NisipeanuAlexandru/Oscilator-RC-cu-Punte-Wien/Simulations/stabilitate(AC).jpg

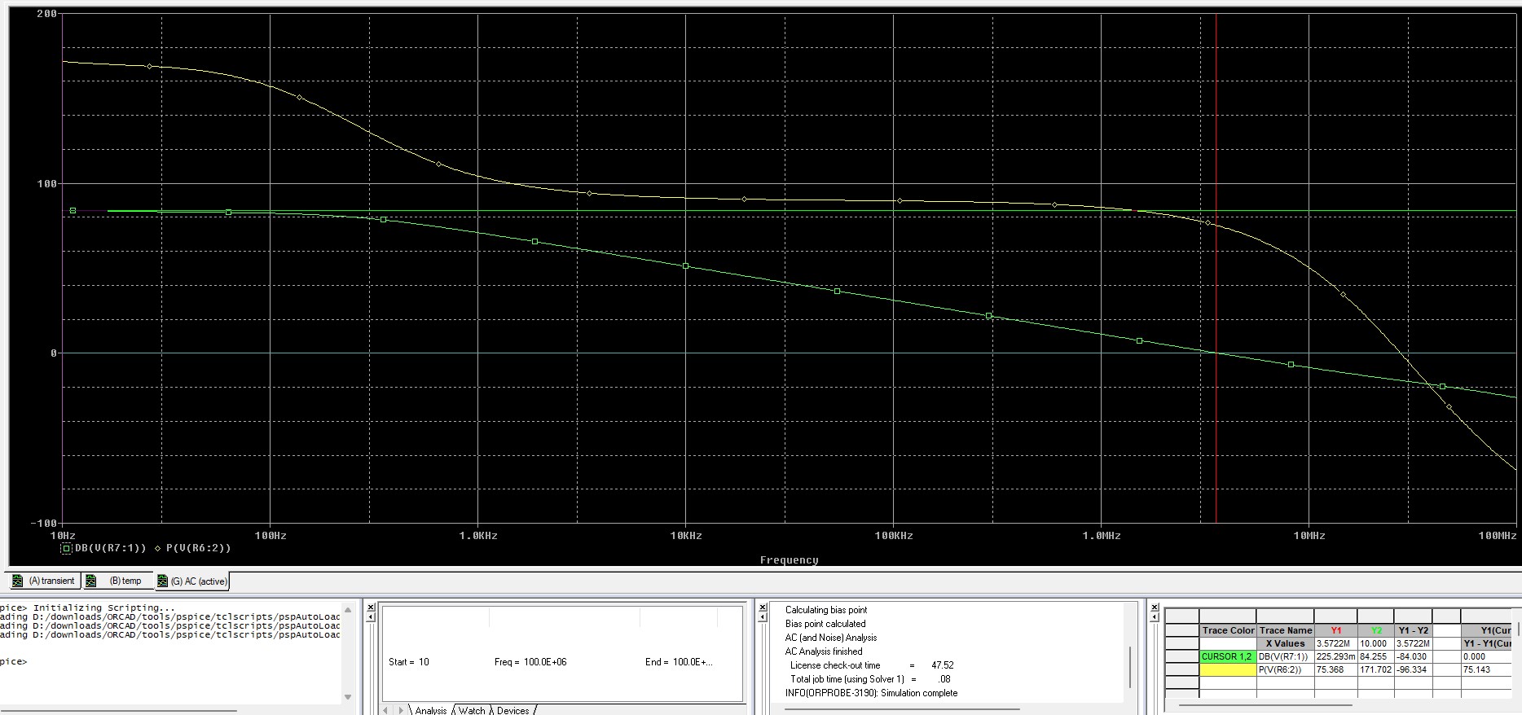
Simulations/stabilitate(AC).jpg
