NisipeanuAlexandru/Oscilator-RC-cu-Punte-Wien/Simulations/stabilitate(AC)_-20_120.jpg

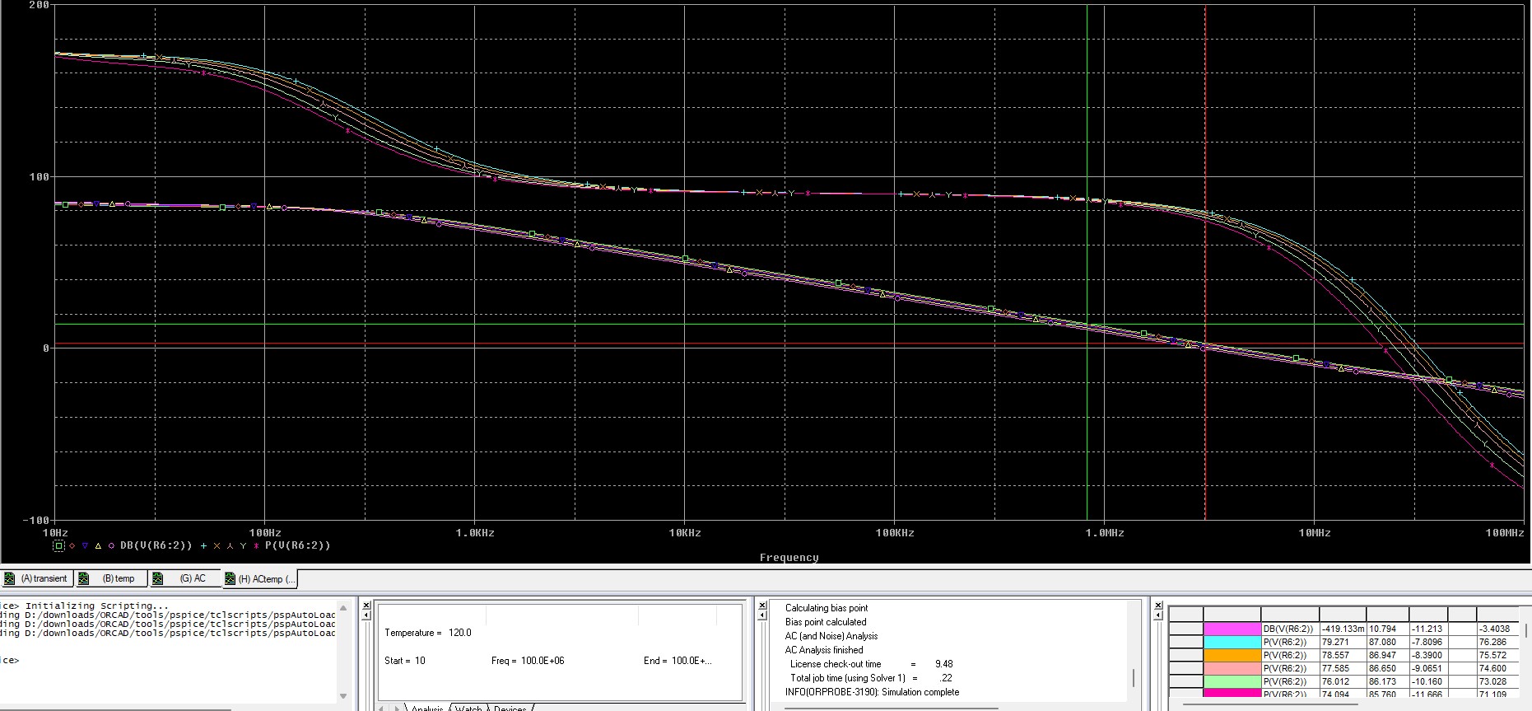
Simulations/stabilitate(AC)_-20_120.jpg
