NisipeanuAlexandru/Oscilator-RC-cu-Punte-Wien/Simulations/transient(zoom)_45KHz.jpg

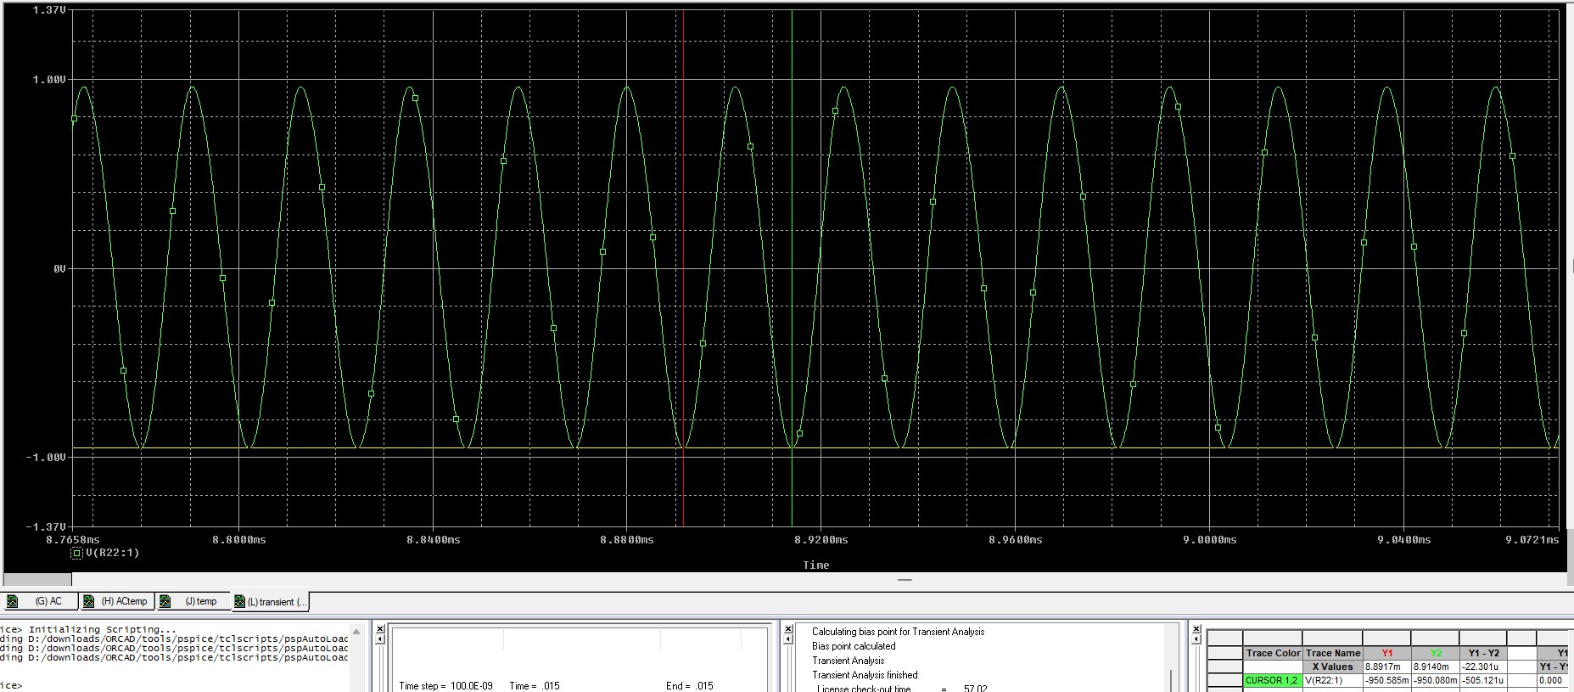
Simulations/transient(zoom)_45KHz.jpg
