NisipeanuAlexandru/Oscilator-RC-cu-Punte-Wien/Simulations/transient_7.7KHz.jpg

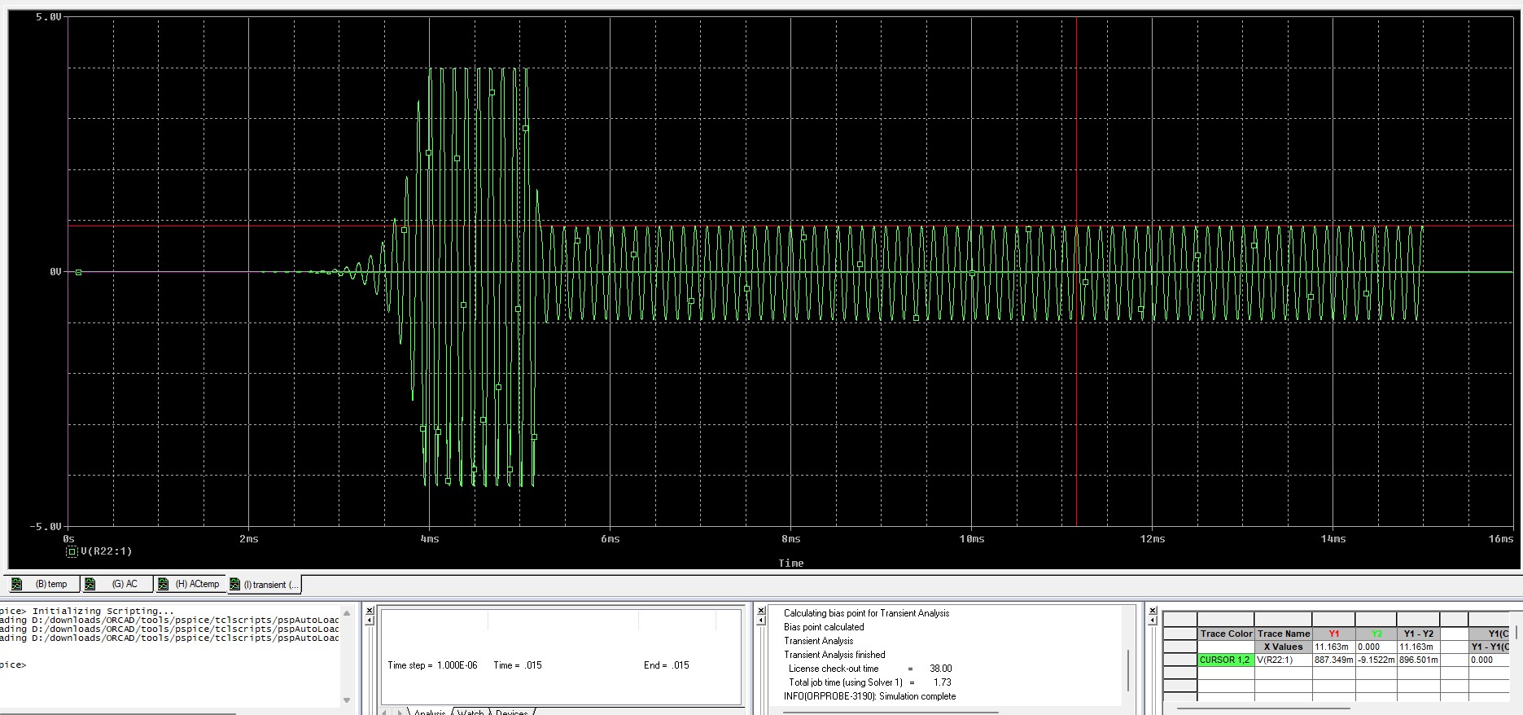
Simulations/transient_7.7KHz.jpg
