NisipeanuAlexandru/Oscilator-RC-cu-Punte-Wien/Simulations/transient_45KHz.jpg

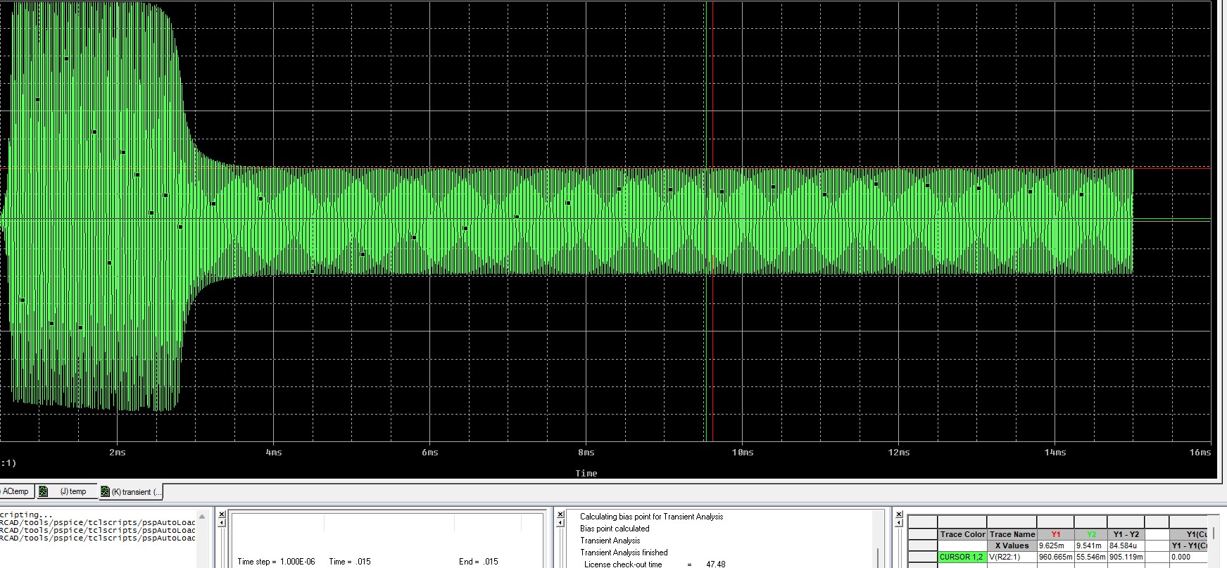
Simulations/transient_45KHz.jpg
